Tinkerforge/evse-v2-bricklet/software/src/evse.c

/* evse-v2-bricklet
 * Copyright (C) 2021 Olaf Lüke <olaf@tinkerforge.com>
 *
 * evse.c: EVSE implementation
 *
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
 * You should have received a copy of the GNU Lesser General Public
 * License along with this library; if not, write to the
 * Free Software Foundation, Inc., 59 Temple Place - Suite 330,
 * Boston, MA 02111-1307, USA.
 */

#include "evse.h"

#include <float.h>

#include "configs/config_evse.h"
#include "bricklib2/hal/ccu4_pwm/ccu4_pwm.h"
#include "bricklib2/hal/system_timer/system_timer.h"
#include "bricklib2/logging/logging.h"
#include "bricklib2/utility/util_definitions.h"
#include "bricklib2/bootloader/bootloader.h"
#include "bricklib2/warp/meter.h"
#include "bricklib2/warp/contactor_check.h"

#include "adc.h"
#include "iec61851.h"
#include "lock.h"
#include "led.h"
#include "dc_fault.h"
#include "communication.h"
#include "charging_slot.h"
#include "button.h"
#include "iec61851.h"
#include "hardware_version.h"
#include "phase_control.h"
#include "ove_r37.h"

#include "xmc_scu.h"
#include "xmc_ccu4.h"
#include "xmc_vadc.h"
#include "xmc_gpio.h"

#define EVSE_RELAY_MONOFLOP_TIME 10000 // 10 seconds

EVSE evse;

static float last_duty_cycle = FLT_MAX;

// Interrupt for debugging
#if 0
#define evse_cp_pwm_irq IRQ_Hdlr_30
void __attribute__((optimize("-O3"))) __attribute__ ((section (".ram_code"))) evse_cp_pwm_irq(void) {
	XMC_VADC_GLOBAL_BackgroundTriggerConversion(VADC);
	XMC_GPIO_SetOutputHigh(EVSE_OUTPUT_GP_PIN);
}
#endif


void evse_set_output(const float cp_duty_cycle, const bool contactor) {
	static uint32_t last_resistance_counter_on_off = 0;
	static uint32_t last_resistance_counter_off_on = 0;
	evse_set_cp_duty_cycle(cp_duty_cycle);

	// If the contactor is to be enabled and the lock is currently
	// not completely closed, we start the locking procedure and return.
	// The contactor will only be enabled after the lock is closed.
#ifdef EVSE_LOCK_ENABLE
	if(contactor) {
		if(lock_get_state() != LOCK_STATE_CLOSE) {
			lock_set_locked(true);
			return;
		}
	}
#endif

	if(((bool)!XMC_GPIO_GetInput(EVSE_CONTACTOR_PIN)) != contactor) {
		if(((cp_duty_cycle == 0) || (cp_duty_cycle == 1000)) && (!contactor) && (last_resistance_counter_off_on == 0) && (last_resistance_counter_on_off == 0)) {
			// If the duty cycle is set to either 0% or 100% PWM and the contactor is supposed to be turned off,
			// it is possible that the WARP Charger wants to turn off the charging session while the car
			// still wants to charge. In this case we wait until the car actually stops charging and
			// changes the resistance back to 2700 ohm before we turn the contactor off.
			// This assures that the contactor is not switched under load.
			//
			// NOTE: In case of an emergency (for example a dc fault detection) the contactor is of course switched off
			//       immediately and directly in the fault detection code without any regard to charging-state,
			//       PWM value, resistance or similar.
			//       This function is only called in non-emergency cases.

			if(adc_result.cp_pe_resistance <= iec61851_get_cp_resistance_threshold(IEC61851_STATE_B)) {
				if(evse.contactor_turn_off_time == 0) {
					evse.contactor_turn_off_time = system_timer_get_ms();
					return;
				} else if(system_timer_is_time_elapsed_ms(evse.contactor_turn_off_time, 6*1000)) {
					// The car has to respond within 3 seconds (see IEC 61851-1 standard table A.6 sequence 10.1).
					// But according to Table A.6 sequence 10.2 the EVSE shall wait 6 seconds to turn the contactor off
					// if the EV does not respond to the change in CP signal. So we wait for 6 seconds here.
					evse.contactor_turn_off_time = 0;
					evse.contactor_maybe_switched_under_load = true;
				} else {
					return;
				}
			} else {
				evse.contactor_turn_off_time = 0;
			}
		}

		if(contactor) {
			// Reset on->off counter
			last_resistance_counter_on_off = 0;

			// If we are asked to turn the contactor on, we first wait for the diode check to finish
			if(iec61851.diode_check_pending) {
				return;
			}
			// If we are asked to turn the contactor on, we want to see at least 500ms worth of adc measurements
			// in a row that supports this conclusion.
			// To do this the ADC code increases a counter every time a new CP/PE resistance is saved.
			// We expect to see 20 consecutive measurements, otherwise we don't turn the contactor on.
			// This is a generic method to ignore glitches that persist for only a few adc measurements.
			// According to IEC 61851-1 standard table A.6 sequence 4, the EVSE is allowed to take 3s for the transation,
			// so there is we are not acutally in a rush here.
			// Additionally, the new iX3 seems to have a feature where it applies the 880 Ohm resistance for about 250ms
			// before immediately going back to 2700 Ohm after a change from 1-phase to 3-phase.
			// We think the BMW tries to to wake up the ISO15118 stack of the EVSE according to
			// IEC 61851-1 table A.6 sequence 11 "EV signal to the EV supply equipment".
			// We don't want to turn the contactor on/off in this case...
			if(last_resistance_counter_off_on == 0) {
				last_resistance_counter_off_on = adc_result.resistance_counter;
				return;
			} else if((uint32_t)(adc_result.resistance_counter - last_resistance_counter_off_on) < 19) { // 19 here is correct, one measurement was alredy done when we reach here
				// We have seen the resistance that results in a off -> on transtion for less than 20 measurements (500ms).
				return;
			} else {
				last_resistance_counter_off_on = 0;
			}
		} else {
			// Reset off->on counter
			last_resistance_counter_off_on = 0;

			// When we turn the contactor off, we need to react in a maximum of 100ms as defined in
			// IEC 61851-1 standard table A.6 sequence 8.1.
			if(last_resistance_counter_on_off == 0) {
				last_resistance_counter_on_off = adc_result.resistance_counter;
				return;
			} else if((uint32_t)(adc_result.resistance_counter - last_resistance_counter_on_off) < 2) { // 2 here is correct, one measurement was alredy done when we reach here
				// We have seen the resistance that results in a off -> on transtion for less than 3 measurements (75ms).
				return;
			} else {
				last_resistance_counter_on_off = 0;
			}
		}
		// Ignore all ADC measurements for a while if the contactor is
		// switched on or off, to be sure that the resulting EMI spike does
		// not give us a wrong measurement.
		adc_ignore_results(8);

		// Also ignore contactor check for a while when contactor changes state
		contactor_check.invalid_counter = MAX(5, contactor_check.invalid_counter);

		if(contactor) {
			// As soon as the contactor is turned on, we are not allowed to switch phases anymore until the car is disconnected.
			iec61851.instant_phase_switch_allowed = false;

			// Reset the "maybe switched under load" flag
			evse.contactor_maybe_switched_under_load = false;

			XMC_GPIO_SetOutputLow(EVSE_CONTACTOR_PIN);
		} else {
			XMC_GPIO_SetOutputHigh(EVSE_CONTACTOR_PIN);
		}

		evse.last_contactor_switch = system_timer_get_ms();
	}

#ifdef EVSE_LOCK_ENABLE
	if(!contactor) {
		if(lock_get_state() != LOCK_STATE_OPEN) {
			lock_set_locked(false);
		}
	}
#endif
}

void evse_load_config(void) {
	uint32_t page[EEPROM_PAGE_SIZE/sizeof(uint32_t)];
	bootloader_read_eeprom_page(EVSE_CONFIG_PAGE, page);

	// The magic number is not where it is supposed to be.
	// This is either our first startup or something went wrong.
	// We initialize the config data with sane default values.
	if(page[EVSE_CONFIG_MAGIC_POS] != EVSE_CONFIG_MAGIC) {
		evse.legacy_managed               = false;
		meter.relative_energy_sum.f       = 0.0f;
		evse.shutdown_input_configuration_old = hardware_version.is_v2 ? EVSE_V2_SHUTDOWN_INPUT_IGNORED : EVSE_V2_SHUTDOWN_INPUT_4200_WATT_ON_CLOSE;
	} else {
		evse.legacy_managed               = page[EVSE_CONFIG_MANAGED_POS];
		meter.relative_energy_sum.data    = page[EVSE_CONFIG_REL_SUM_POS];
		evse.shutdown_input_configuration_old = page[EVSE_CONFIG_SHUTDOWN_INPUT_POS];
	}

	if(page[EVSE_CONFIG_MAGIC2_POS] != EVSE_CONFIG_MAGIC2) {
		evse.input_configuration          = 0;
		evse.output_configuration         = EVSE_V2_OUTPUT_HIGH_IMPEDANCE;
		button.configuration              = EVSE_V2_BUTTON_CONFIGURATION_STOP_CHARGING;
	} else {
		evse.input_configuration          = page[EVSE_CONFIG_INPUT_POS];
		evse.output_configuration         = page[EVSE_CONFIG_OUTPUT_POS];
		button.configuration              = page[EVSE_CONFIG_BUTTON_POS];
	}

	if(page[EVSE_CONFIG_MAGIC3_POS] != EVSE_CONFIG_MAGIC3) {
		evse.boost_mode_enabled           = false;
		evse.ev_wakeup_enabled            = true;
	} else {
		evse.boost_mode_enabled           = page[EVSE_CONFIG_BOOST_POS];
		evse.ev_wakeup_enabled            = page[EVSE_CONFIG_EV_WAKUEP_POS];
	}

	if(page[EVSE_CONFIG_MAGIC4_POS] != EVSE_CONFIG_MAGIC4) {
		meter.relative_energy_import.f    = 0.0f;
		meter.relative_energy_export.f    = 0.0f;
	} else {
		meter.relative_energy_import.data = page[EVSE_CONFIG_REL_IMPORT_POS];
		meter.relative_energy_export.data = page[EVSE_CONFIG_REL_EXPORT_POS];
	}

	if(page[EVSE_CONFIG_MAGIC5_POS] != EVSE_CONFIG_MAGIC5) {
		phase_control.autoswitch_enabled = true;
		phase_control.phases_connected   = 3;
	} else {
		phase_control.autoswitch_enabled = page[EVSE_CONFIG_AUTOSWITCH_POS];
		phase_control.phases_connected   = (page[EVSE_CONFIG_PHASES_CON_POS] == 1) ? 1 : 3;
	}

	bool external_control_slot_to_default = false;
	// We use MAGIC6 to check if the new handling for external control is already active.
	// If the magic is not set, we activate the external control slot and set proper default values.
	// After that we set the new magic, so this only happens after first update.
	if(page[EVSE_CONFIG_MAGIC6_POS] != EVSE_CONFIG_MAGIC6) {
		external_control_slot_to_default = true;
	}

	if(page[EVSE_CONFIG_MAGIC7_POS] != EVSE_CONFIG_MAGIC7) {
		phase_control.phase_switch_wait_time = EVSE_V2_PHASE_SWITCH_WAIT_TIME_DEFAULT;
	} else {
		phase_control.phase_switch_wait_time = page[EVSE_CONFIG_PS_WAIT_TIME_POS];
	}

	if(page[EVSE_CONFIG_MAGIC8_POS] != EVSE_CONFIG_MAGIC8) {
		evse.shutdown_input_configuration = evse.shutdown_input_configuration_old;
	} else {
		evse.shutdown_input_configuration = page[EVSE_CONFIG_SHUTDOWN_INPUT2_POS];
	}

	if(page[EVSE_CONFIG_MAGIC9_POS] == EVSE_CONFIG_MAGIC9) {
		ove_r37.enabled                   = page[EVSE_CONFIG_OVE_R37_ENABLED_POS];
		ove_r37.undervoltage_threshold_pu = page[EVSE_CONFIG_OVE_R37_UV_THRESHOLD_POS];
		ove_r37.undervoltage_observe_ms   = page[EVSE_CONFIG_OVE_R37_UV_OBSERVE_POS];
		ove_r37.reconnect_wait_s          = page[EVSE_CONFIG_OVE_R37_RECONNECT_WAIT_POS];
	}

	// Handle charging slot defaults
	EVSEChargingSlotDefault *slot_default = (EVSEChargingSlotDefault *)(&page[EVSE_CONFIG_SLOT_DEFAULT_POS]);
	if(slot_default->magic == EVSE_CONFIG_SLOT_MAGIC) {
		for(uint8_t i = 0; i < 18; i++) {
			charging_slot.max_current_default[i]         = slot_default->current[i];
			charging_slot.active_default[i]              = slot_default->active_clear[i] & 1;
			charging_slot.clear_on_disconnect_default[i] = slot_default->active_clear[i] & 2;
		}
	} else {
		// If there is no default the button slot is activated and everything else is deactivated
		for(uint8_t i = 0; i < 18; i++) {
			charging_slot.max_current_default[i]         = 32000;
			charging_slot.active_default[i]              = false;
			charging_slot.clear_on_disconnect_default[i] = false;
		}

		// The default indices are offset by 2 to the slot indices
		charging_slot.max_current_default[CHARGING_SLOT_BUTTON-2]         = 32000;
		charging_slot.active_default[CHARGING_SLOT_BUTTON-2]              = true;
		charging_slot.clear_on_disconnect_default[CHARGING_SLOT_BUTTON-2] = false;

		charging_slot.max_current_default[CHARGING_SLOT_LOAD_MANAGEMENT-2]         = 0;
		charging_slot.active_default[CHARGING_SLOT_LOAD_MANAGEMENT-2]              = evse.legacy_managed;
		charging_slot.clear_on_disconnect_default[CHARGING_SLOT_LOAD_MANAGEMENT-2] = evse.legacy_managed;
	}

	if(external_control_slot_to_default) {
		charging_slot.max_current_default[CHARGING_SLOT_EXTERNAL-2]         = 32000;
		charging_slot.active_default[CHARGING_SLOT_EXTERNAL-2]              = false;
		charging_slot.clear_on_disconnect_default[CHARGING_SLOT_EXTERNAL-2] = false;
	}

	logd("Load config:\n\r");
	logd(" * legacy managed    %d\n\r", evse.legacy_managed);
	logd(" * relener           %d %d %d\n\r", meter.relative_energy_sum.data, meter.relative_energy_import.data, meter.relative_energy_export.data);
	logd(" * shutdown input    %d\n\r", evse.shutdown_input_configuration);
	logd(" * slot current      %d %d %d %d %d %d %d %d\n\r", charging_slot.max_current_default[0], charging_slot.max_current_default[1], charging_slot.max_current_default[2], charging_slot.max_current_default[3], charging_slot.max_current_default[4], charging_slot.max_current_default[5], charging_slot.max_current_default[6], charging_slot.max_current_default[7]);
	logd(" * slot active/clear %d %d %d %d %d %d %d %d\n\r", charging_slot.clear_on_disconnect_default[0], charging_slot.clear_on_disconnect_default[1], charging_slot.clear_on_disconnect_default[2], charging_slot.clear_on_disconnect_default[3], charging_slot.clear_on_disconnect_default[4], charging_slot.clear_on_disconnect_default[5], charging_slot.clear_on_disconnect_default[6], charging_slot.clear_on_disconnect_default[7]);
}

void evse_save_config(void) {
	// In old firmwares the page buffer is not zeroed.
	// If we downgrade from this firmware to an old firmware we were able to reproducible
	// get the "EVSE_CONFIG_MAGIC8" in the correct page index as uninitialized stack memory.
	// We put a new value above the page and print it (so the compiler can't possibly remove it),
	// to make sure that we can't accidentially leak the magic from a new firmware into an firmware.
	uint8_t random_val = system_timer_get_ms() % 255;
	uint32_t page[EEPROM_PAGE_SIZE/sizeof(uint32_t)] = {0};
	logd("random_val %d\n\r", random_val);

	page[EVSE_CONFIG_MAGIC_POS]           = EVSE_CONFIG_MAGIC;
	page[EVSE_CONFIG_MANAGED_POS]         = evse.legacy_managed;
	page[EVSE_CONFIG_SHUTDOWN_INPUT_POS]  = evse.shutdown_input_configuration_old;
	if(meter.reset_energy_meter) {
		page[EVSE_CONFIG_REL_SUM_POS]     = meter_register_set.EnergyActiveLSumImExSum.data;
		page[EVSE_CONFIG_REL_IMPORT_POS]  = meter_register_set.EnergyActiveLSumImport.data;
		page[EVSE_CONFIG_REL_EXPORT_POS]  = meter_register_set.EnergyActiveLSumExport.data;
		meter.relative_energy_sum.data    = meter_register_set.EnergyActiveLSumImExSum.data;
		meter.relative_energy_import.data = meter_register_set.EnergyActiveLSumImport.data;
		meter.relative_energy_export.data = meter_register_set.EnergyActiveLSumExport.data;
	} else {
		page[EVSE_CONFIG_REL_SUM_POS]     = meter.relative_energy_sum.data;
		page[EVSE_CONFIG_REL_IMPORT_POS]  = meter.relative_energy_import.data;
		page[EVSE_CONFIG_REL_EXPORT_POS]  = meter.relative_energy_export.data;
	}
	meter.reset_energy_meter = false;

	page[EVSE_CONFIG_MAGIC2_POS]          = EVSE_CONFIG_MAGIC2;
	page[EVSE_CONFIG_INPUT_POS]           = evse.input_configuration;
	page[EVSE_CONFIG_OUTPUT_POS]          = evse.output_configuration;
	page[EVSE_CONFIG_BUTTON_POS]          = button.configuration;

	page[EVSE_CONFIG_MAGIC3_POS]          = EVSE_CONFIG_MAGIC3;
	page[EVSE_CONFIG_BOOST_POS]           = evse.boost_mode_enabled;
	page[EVSE_CONFIG_EV_WAKUEP_POS]       = evse.ev_wakeup_enabled;

	page[EVSE_CONFIG_MAGIC4_POS]          = EVSE_CONFIG_MAGIC4;

	page[EVSE_CONFIG_MAGIC5_POS]          = EVSE_CONFIG_MAGIC5;
	page[EVSE_CONFIG_AUTOSWITCH_POS]      = phase_control.autoswitch_enabled;
	page[EVSE_CONFIG_PHASES_CON_POS]      = phase_control.phases_connected;

	page[EVSE_CONFIG_MAGIC6_POS]          = EVSE_CONFIG_MAGIC6;

	page[EVSE_CONFIG_MAGIC7_POS]          = EVSE_CONFIG_MAGIC7;
	page[EVSE_CONFIG_PS_WAIT_TIME_POS]    = phase_control.phase_switch_wait_time;

	page[EVSE_CONFIG_MAGIC8_POS]          = EVSE_CONFIG_MAGIC8;
	page[EVSE_CONFIG_SHUTDOWN_INPUT2_POS] = evse.shutdown_input_configuration;

	page[EVSE_CONFIG_MAGIC9_POS]                 = EVSE_CONFIG_MAGIC9;
	page[EVSE_CONFIG_OVE_R37_ENABLED_POS]        = ove_r37.enabled;
	page[EVSE_CONFIG_OVE_R37_UV_THRESHOLD_POS]   = ove_r37.undervoltage_threshold_pu;
	page[EVSE_CONFIG_OVE_R37_UV_OBSERVE_POS]     = ove_r37.undervoltage_observe_ms;
	page[EVSE_CONFIG_OVE_R37_RECONNECT_WAIT_POS] = ove_r37.reconnect_wait_s;
	page[EVSE_CONFIG_OVE_R37_START_DELAY_POS]    = 0;

	// Handle charging slot defaults
	EVSEChargingSlotDefault *slot_default = (EVSEChargingSlotDefault *)(&page[EVSE_CONFIG_SLOT_DEFAULT_POS]);
	for(uint8_t i = 0; i < 18; i++) {
		slot_default->current[i]      = charging_slot.max_current_default[i];
		slot_default->active_clear[i] = (charging_slot.active_default[i] << 0) | (charging_slot.clear_on_disconnect_default[i] << 1);
	}
	slot_default->magic = EVSE_CONFIG_SLOT_MAGIC;

	bootloader_write_eeprom_page(EVSE_CONFIG_PAGE, page);
}

void evse_factory_reset(void) {
	uint32_t page[EEPROM_PAGE_SIZE/sizeof(uint32_t)] = {0};
	bootloader_write_eeprom_page(EVSE_CONFIG_PAGE, page);

	NVIC_SystemReset();
}

uint16_t evse_get_cp_pwm_duty_cycle(void) {
	return XMC_CCU4_SLICE_GetTimerCompareMatch(hardware_version.is_v2 ? CCU40_CC40 : CCU41_CC40);
}

uint16_t evse_get_cp_duty_cycle(void) {
	if(iec61851.test_mode_no_pwm) {
		return (uint16_t)last_duty_cycle;
	}
	uint16_t duty_cycle = (uint16_t)((48000 - evse_get_cp_pwm_duty_cycle())/48.0 + 0.5);
	if((duty_cycle >= EVSE_BOOST_MODE_US) && (duty_cycle != 1000) && (duty_cycle != 0) && evse.boost_mode_enabled) {
		return duty_cycle - EVSE_BOOST_MODE_US;
	}

	return duty_cycle;
}

void evse_set_cp_duty_cycle(const float duty_cycle) {
	if(iec61851.test_mode_no_pwm) {
		last_duty_cycle = duty_cycle;
		return;
	}
	if(((last_duty_cycle == 1000)) && ((duty_cycle > 0) && (duty_cycle < 1000)) && (iec61851.charging_protocol != EVSE_V2_CHARGING_PROTOCOL_ISO15118)) {
		iec61851.state_b1b2_transition_seen = true;
	}
	if(last_duty_cycle != duty_cycle) {
		// Ignore ADC results for ~550ms after PWM change
		// We have seen in several hybrid BMW cars that they have a 2700 ohm resistance glitch on
		// the CP line after about 500ms after a change of the duty cycle....
		if((duty_cycle != 1000) && (duty_cycle != 0) && (last_duty_cycle != 1000) && (last_duty_cycle != 0)) {
			adc_ignore_results(22);
		}
		evse.last_duty_cycle_change_time = system_timer_get_ms();
		last_duty_cycle = duty_cycle;
	}

	// According to IEC 61851-1 table A.2 the duty cycle is allowed to be off by up to 5us.
	// If boost mode is enabled we add 4us to the duty cycle. This means that we are still within the standard.
	uint16_t adc_boost = 0;
	if((duty_cycle != 0) && (duty_cycle != 1000) && evse.boost_mode_enabled) {
		adc_boost = EVSE_BOOST_MODE_US;
	}

	// Note: We must not compare against evse_get_cp_pwm_duty_cycle() here to find out if
	// the compare value has to be updated. XMC_CCU4_SLICE_SetTimerCompareMatch() writes the
	// shadow register (CRS), while XMC_CCU4_SLICE_GetTimerCompareMatch() reads the active
	// register (CR), which is only updated on the next period match (up to 1ms later).
	static uint16_t last_written_cp_duty_cycle = 0xFFFF; // impossible value (valid range 0-48000)
	const uint16_t new_cp_duty_cycle = (uint16_t)(48000 - (duty_cycle + adc_boost)*48 + 0.5f);

	if(last_written_cp_duty_cycle != new_cp_duty_cycle) {
		last_written_cp_duty_cycle = new_cp_duty_cycle;

		adc_enable_all(duty_cycle > 999.99f);

		// EVSE V2 uses CCU40, EVSE V3 and V4 uses CCU41
		XMC_CCU4_SLICE_SetTimerCompareMatch(hardware_version.is_v2 ? CCU40_CC40 : CCU41_CC40, new_cp_duty_cycle);
		XMC_CCU4_EnableShadowTransfer(hardware_version.is_v2 ? CCU40 : CCU41, XMC_CCU4_SHADOW_TRANSFER_SLICE_0 | XMC_CCU4_SHADOW_TRANSFER_PRESCALER_SLICE_0);
	}
}

// Check pin header for max current
void evse_init_jumper(void) {
	const XMC_GPIO_CONFIG_t pin_config_input_tristate = {
		.mode             = XMC_GPIO_MODE_INPUT_TRISTATE,
		.input_hysteresis = XMC_GPIO_INPUT_HYSTERESIS_STANDARD
	};

	const XMC_GPIO_CONFIG_t pin_config_input_pullup = {
		.mode             = XMC_GPIO_MODE_INPUT_PULL_UP,
		.input_hysteresis = XMC_GPIO_INPUT_HYSTERESIS_STANDARD
	};

	const XMC_GPIO_CONFIG_t pin_config_input_pulldown = {
		.mode             = XMC_GPIO_MODE_INPUT_PULL_DOWN,
		.input_hysteresis = XMC_GPIO_INPUT_HYSTERESIS_STANDARD
	};

	XMC_GPIO_Init(EVSE_CONFIG_JUMPER_PIN0, &pin_config_input_pullup);
	XMC_GPIO_Init(EVSE_CONFIG_JUMPER_PIN1, &pin_config_input_pullup);
	system_timer_sleep_ms(50);
	bool pin0_pu = XMC_GPIO_GetInput(EVSE_CONFIG_JUMPER_PIN0);
	bool pin1_pu = XMC_GPIO_GetInput(EVSE_CONFIG_JUMPER_PIN1);

	XMC_GPIO_Init(EVSE_CONFIG_JUMPER_PIN0, &pin_config_input_pulldown);
	XMC_GPIO_Init(EVSE_CONFIG_JUMPER_PIN1, &pin_config_input_pulldown);
	system_timer_sleep_ms(50);
	bool pin0_pd = XMC_GPIO_GetInput(EVSE_CONFIG_JUMPER_PIN0);
	bool pin1_pd = XMC_GPIO_GetInput(EVSE_CONFIG_JUMPER_PIN1);

	XMC_GPIO_Init(EVSE_CONFIG_JUMPER_PIN0, &pin_config_input_tristate);
	XMC_GPIO_Init(EVSE_CONFIG_JUMPER_PIN1, &pin_config_input_tristate);

	// Differentiate between high, low and open
	char pin0 = 'x';
	if(pin0_pu && !pin0_pd) {
		pin0 = 'o';
	} else if(pin0_pu && pin0_pd) {
		pin0 = 'h';
	} else if(!pin0_pu && !pin0_pd) {
		pin0 = 'l';
	}

	char pin1 = 'x';
	if(pin1_pu && !pin1_pd) {
		pin1 = 'o';
	} else if(pin1_pu && pin1_pd) {
		pin1 = 'h';
	} else if(!pin1_pu && !pin1_pd) {
		pin1 = 'l';
	}

	if(hardware_version.is_v2) {
		if(pin0 == 'h' && pin1 == 'h') {
			evse.config_jumper_current = EVSE_CONFIG_JUMPER_RESERVED;
		} else if(pin0 == 'o' && pin1 == 'h') {
			evse.config_jumper_current = EVSE_CONFIG_JUMPER_CURRENT_32A;
		} else if(pin0 == 'l' && pin1 == 'h') {
			evse.config_jumper_current = EVSE_CONFIG_JUMPER_CURRENT_25A;
		} else if(pin0 == 'h' && pin1 == 'o') {
			evse.config_jumper_current = EVSE_CONFIG_JUMPER_CURRENT_20A;
		} else if(pin0 == 'o' && pin1 == 'o') {
			evse.config_jumper_current = EVSE_CONFIG_JUMPER_CURRENT_16A;
		} else if(pin0 == 'l' && pin1 == 'o') {
			evse.config_jumper_current = EVSE_CONFIG_JUMPER_CURRENT_13A;
		} else if(pin0 == 'h' && pin1 == 'l') {
			evse.config_jumper_current = EVSE_CONFIG_JUMPER_CURRENT_10A;
		} else if(pin0 == 'o' && pin1 == 'l') {
			evse.config_jumper_current = EVSE_CONFIG_JUMPER_CURRENT_6A;
		} else {
			evse.config_jumper_current = EVSE_CONFIG_JUMPER_UNCONFIGURED;
		}
	} else { // v3 or v4
		if(pin0 == 'h' && pin1 == 'h') {
			evse.config_jumper_current = EVSE_CONFIG_JUMPER_CURRENT_32A;
		} else if(pin0 == 'o' && pin1 == 'h') {
			evse.config_jumper_current = EVSE_CONFIG_JUMPER_RESERVED;
		} else if(pin0 == 'l' && pin1 == 'h') {
			evse.config_jumper_current = EVSE_CONFIG_JUMPER_CURRENT_25A;
		} else if(pin0 == 'h' && pin1 == 'o') {
			evse.config_jumper_current = EVSE_CONFIG_JUMPER_CURRENT_13A;
		} else if(pin0 == 'o' && pin1 == 'o') {
			evse.config_jumper_current = EVSE_CONFIG_JUMPER_UNCONFIGURED;
		} else if(pin0 == 'l' && pin1 == 'o') {
			evse.config_jumper_current = EVSE_CONFIG_JUMPER_CURRENT_6A;
		} else if(pin0 == 'h' && pin1 == 'l') {
			evse.config_jumper_current = EVSE_CONFIG_JUMPER_CURRENT_20A;
		} else if(pin0 == 'o' && pin1 == 'l') {
			evse.config_jumper_current = EVSE_CONFIG_JUMPER_CURRENT_10A;
		} else if(pin0 == 'l' && pin1 == 'l') {
			evse.config_jumper_current = EVSE_CONFIG_JUMPER_CURRENT_16A;
		} else {
			evse.config_jumper_current = EVSE_CONFIG_JUMPER_UNCONFIGURED;
		}
	}
}

// Use CCU40 slice 0 for CP/PE
// Use CCU40 slice 1 synchronously with slice 0 but with fixed duty-cycle
// Slice 1 is used to generate IRQ for ADC measurements to make sure that CP/PE PWM high level is measured at end of duty-cycle
void evse_v2_init_cp_pwm(void) {
	const XMC_CCU4_SLICE_COMPARE_CONFIG_t compare_config = {
		.timer_mode          = XMC_CCU4_SLICE_TIMER_COUNT_MODE_EA,
		.monoshot            = false,
		.shadow_xfer_clear   = 0,
		.dither_timer_period = 0,
		.dither_duty_cycle   = 0,
		.prescaler_mode      = XMC_CCU4_SLICE_PRESCALER_MODE_NORMAL,
		.mcm_enable          = 0,
		.prescaler_initval   = XMC_CCU4_SLICE_PRESCALER_2,
		.float_limit         = 0,
		.dither_limit        = 0,
		.passive_level       = XMC_CCU4_SLICE_OUTPUT_PASSIVE_LEVEL_LOW,
		.timer_concatenation = 0
	};

 	const XMC_CCU4_SLICE_EVENT_CONFIG_t event_config = {
		 .duration = XMC_CCU4_SLICE_EVENT_FILTER_5_CYCLES,
		 .edge = XMC_CCU4_SLICE_EVENT_EDGE_SENSITIVITY_RISING_EDGE,
		 .level = XMC_CCU4_SLICE_EVENT_LEVEL_SENSITIVITY_ACTIVE_HIGH,
		 .mapped_input = XMC_CCU4_SLICE_INPUT_AI
	};

	const XMC_GPIO_CONFIG_t gpio_out_config	= {
		.mode                = XMC_GPIO_MODE_OUTPUT_PUSH_PULL_ALT2,
		.input_hysteresis    = XMC_GPIO_INPUT_HYSTERESIS_STANDARD,
		.output_level        = XMC_GPIO_OUTPUT_LEVEL_LOW,
	};

	XMC_CCU4_Init(CCU40, XMC_CCU4_SLICE_MCMS_ACTION_TRANSFER_PR_CR);
	XMC_CCU4_StartPrescaler(CCU40);
	XMC_CCU4_SLICE_CompareInit(CCU40_CC40, &compare_config);
	XMC_CCU4_SLICE_CompareInit(CCU40_CC41, &compare_config);
	XMC_CCU4_SLICE_CompareInit(CCU40_CC42, &compare_config);

	// Set the period and compare register values
	XMC_CCU4_SLICE_SetTimerPeriodMatch(CCU40_CC40, EVSE_CP_PWM_PERIOD-1);
	XMC_CCU4_SLICE_SetTimerPeriodMatch(CCU40_CC41, EVSE_CP_PWM_PERIOD-1);
	XMC_CCU4_SLICE_SetTimerPeriodMatch(CCU40_CC42, EVSE_CP_PWM_PERIOD-1);
	XMC_CCU4_SLICE_SetTimerCompareMatch(CCU40_CC40, 48000 - 0*48);
	XMC_CCU4_SLICE_SetTimerCompareMatch(CCU40_CC41, 48000 - 30*48); // 3% duty-cycle (this puts the first ADC measurement at the end of the high part of the PWM)
	XMC_CCU4_SLICE_SetTimerCompareMatch(CCU40_CC42, 48000 - 750*48); // 75% duty-cycle (this puts the second ADC measurement at the middle the low part of the PWM)

	XMC_CCU4_EnableShadowTransfer(CCU40, XMC_CCU4_SHADOW_TRANSFER_SLICE_0 | XMC_CCU4_SHADOW_TRANSFER_PRESCALER_SLICE_0 | XMC_CCU4_SHADOW_TRANSFER_SLICE_1 | XMC_CCU4_SHADOW_TRANSFER_PRESCALER_SLICE_1 | XMC_CCU4_SHADOW_TRANSFER_SLICE_2 | XMC_CCU4_SHADOW_TRANSFER_PRESCALER_SLICE_2);

	XMC_GPIO_Init(EVSE_CP_PWM_PIN, &gpio_out_config);

	XMC_CCU4_EnableClock(CCU40, 0);
	XMC_CCU4_EnableClock(CCU40, 1);
	XMC_CCU4_EnableClock(CCU40, 2);

	// Start CCU40 slice 0, 1 and 2 in sync.
	XMC_CCU4_SLICE_ConfigureEvent(CCU40_CC40, XMC_CCU4_SLICE_EVENT_1, &event_config);
	XMC_CCU4_SLICE_ConfigureEvent(CCU40_CC41, XMC_CCU4_SLICE_EVENT_1, &event_config);
	XMC_CCU4_SLICE_ConfigureEvent(CCU40_CC42, XMC_CCU4_SLICE_EVENT_1, &event_config);
	XMC_CCU4_SLICE_StartConfig(CCU40_CC40, XMC_CCU4_SLICE_EVENT_1, XMC_CCU4_SLICE_START_MODE_TIMER_START_CLEAR);
	XMC_CCU4_SLICE_StartConfig(CCU40_CC41, XMC_CCU4_SLICE_EVENT_1, XMC_CCU4_SLICE_START_MODE_TIMER_START_CLEAR);
	XMC_CCU4_SLICE_StartConfig(CCU40_CC42, XMC_CCU4_SLICE_EVENT_1, XMC_CCU4_SLICE_START_MODE_TIMER_START_CLEAR);
	XMC_SCU_SetCcuTriggerHigh(SCU_GENERAL_CCUCON_GSC40_Msk);

	// Enable interrupt for CP PWM (on slice 1)
	XMC_CCU4_SLICE_EnableEvent(CCU40_CC41, XMC_CCU4_SLICE_IRQ_ID_COMPARE_MATCH_UP);
	XMC_CCU4_SLICE_SetInterruptNode(CCU40_CC41, XMC_CCU4_SLICE_IRQ_ID_COMPARE_MATCH_UP, XMC_CCU4_SLICE_SR_ID_2);

	// Enable interrupt for CP PWM (on slice 2)
	XMC_CCU4_SLICE_EnableEvent(CCU40_CC42, XMC_CCU4_SLICE_IRQ_ID_COMPARE_MATCH_UP);
	XMC_CCU4_SLICE_SetInterruptNode(CCU40_CC42, XMC_CCU4_SLICE_IRQ_ID_COMPARE_MATCH_UP, XMC_CCU4_SLICE_SR_ID_2);

	evse_set_cp_duty_cycle(1000.0);

	// Interrupt for debugging, uncomment if needed
//	NVIC_SetPriority(30, 1);
//	XMC_SCU_SetInterruptControl(30, XMC_SCU_IRQCTRL_CCU40_SR2_IRQ30);
//	NVIC_EnableIRQ(30);
}

void evse_v3_init_cp_pwm(void) {
	const XMC_CCU4_SLICE_COMPARE_CONFIG_t compare_config = {
		.timer_mode          = XMC_CCU4_SLICE_TIMER_COUNT_MODE_EA,
		.monoshot            = false,
		.shadow_xfer_clear   = 0,
		.dither_timer_period = 0,
		.dither_duty_cycle   = 0,
		.prescaler_mode      = XMC_CCU4_SLICE_PRESCALER_MODE_NORMAL,
		.mcm_enable          = 0,
		.prescaler_initval   = XMC_CCU4_SLICE_PRESCALER_2,
		.float_limit         = 0,
		.dither_limit        = 0,
		.passive_level       = XMC_CCU4_SLICE_OUTPUT_PASSIVE_LEVEL_LOW,
		.timer_concatenation = 0
	};

 	const XMC_CCU4_SLICE_EVENT_CONFIG_t event_config = {
		 .duration = XMC_CCU4_SLICE_EVENT_FILTER_5_CYCLES,
		 .edge = XMC_CCU4_SLICE_EVENT_EDGE_SENSITIVITY_RISING_EDGE,
		 .level = XMC_CCU4_SLICE_EVENT_LEVEL_SENSITIVITY_ACTIVE_HIGH,
		 .mapped_input = XMC_CCU4_SLICE_INPUT_AI
	};

	const XMC_GPIO_CONFIG_t gpio_out_config	= {
		.mode                = XMC_GPIO_MODE_OUTPUT_PUSH_PULL_ALT9,
		.input_hysteresis    = XMC_GPIO_INPUT_HYSTERESIS_STANDARD,
		.output_level        = XMC_GPIO_OUTPUT_LEVEL_LOW,
	};

	XMC_CCU4_Init(CCU41, XMC_CCU4_SLICE_MCMS_ACTION_TRANSFER_PR_CR);
	XMC_CCU4_StartPrescaler(CCU41);
	XMC_CCU4_SLICE_CompareInit(CCU41_CC40, &compare_config);
	XMC_CCU4_SLICE_CompareInit(CCU41_CC41, &compare_config);
	XMC_CCU4_SLICE_CompareInit(CCU41_CC42, &compare_config);

	// Set the period and compare register values
	XMC_CCU4_SLICE_SetTimerPeriodMatch(CCU41_CC40, EVSE_CP_PWM_PERIOD-1);
	XMC_CCU4_SLICE_SetTimerPeriodMatch(CCU41_CC41, EVSE_CP_PWM_PERIOD-1);
	XMC_CCU4_SLICE_SetTimerPeriodMatch(CCU41_CC42, EVSE_CP_PWM_PERIOD-1);
	XMC_CCU4_SLICE_SetTimerCompareMatch(CCU41_CC40, 48000 - 0*48);
	XMC_CCU4_SLICE_SetTimerCompareMatch(CCU41_CC41, 48000 - 30*48); // 3% duty-cycle (this puts the first ADC measurement at the end of the high part of the PWM)
	XMC_CCU4_SLICE_SetTimerCompareMatch(CCU41_CC42, 48000 - 750*48); // 75% duty-cycle (this puts the second ADC measurement at the middle the low part of the PWM)

	XMC_CCU4_EnableShadowTransfer(CCU41, XMC_CCU4_SHADOW_TRANSFER_SLICE_0 | XMC_CCU4_SHADOW_TRANSFER_PRESCALER_SLICE_0 | XMC_CCU4_SHADOW_TRANSFER_SLICE_1 | XMC_CCU4_SHADOW_TRANSFER_PRESCALER_SLICE_1 | XMC_CCU4_SHADOW_TRANSFER_SLICE_2 | XMC_CCU4_SHADOW_TRANSFER_PRESCALER_SLICE_2);

	XMC_GPIO_Init(EVSE_CP_PWM_PIN, &gpio_out_config);

	XMC_CCU4_EnableClock(CCU41, 0);
	XMC_CCU4_EnableClock(CCU41, 1);
	XMC_CCU4_EnableClock(CCU41, 2);

	// Start CCU41 slice 0, 1 and 2 in sync.
	XMC_CCU4_SLICE_ConfigureEvent(CCU41_CC40, XMC_CCU4_SLICE_EVENT_1, &event_config);
	XMC_CCU4_SLICE_ConfigureEvent(CCU41_CC41, XMC_CCU4_SLICE_EVENT_1, &event_config);
	XMC_CCU4_SLICE_ConfigureEvent(CCU41_CC42, XMC_CCU4_SLICE_EVENT_1, &event_config);
	XMC_CCU4_SLICE_StartConfig(CCU41_CC40, XMC_CCU4_SLICE_EVENT_1, XMC_CCU4_SLICE_START_MODE_TIMER_START_CLEAR);
	XMC_CCU4_SLICE_StartConfig(CCU41_CC41, XMC_CCU4_SLICE_EVENT_1, XMC_CCU4_SLICE_START_MODE_TIMER_START_CLEAR);
	XMC_CCU4_SLICE_StartConfig(CCU41_CC42, XMC_CCU4_SLICE_EVENT_1, XMC_CCU4_SLICE_START_MODE_TIMER_START_CLEAR);
	XMC_SCU_SetCcuTriggerHigh(SCU_GENERAL_CCUCON_GSC41_Msk);

	// Enable interrupt for CP PWM (on slice 1)
	XMC_CCU4_SLICE_EnableEvent(CCU41_CC41, XMC_CCU4_SLICE_IRQ_ID_COMPARE_MATCH_UP);
	XMC_CCU4_SLICE_SetInterruptNode(CCU41_CC41, XMC_CCU4_SLICE_IRQ_ID_COMPARE_MATCH_UP, XMC_CCU4_SLICE_SR_ID_2);

	// Enable interrupt for CP PWM (on slice 2)
	XMC_CCU4_SLICE_EnableEvent(CCU41_CC42, XMC_CCU4_SLICE_IRQ_ID_COMPARE_MATCH_UP);
	XMC_CCU4_SLICE_SetInterruptNode(CCU41_CC42, XMC_CCU4_SLICE_IRQ_ID_COMPARE_MATCH_UP, XMC_CCU4_SLICE_SR_ID_2);

	evse_set_cp_duty_cycle(1000.0);

	// Interrupt for debugging, uncomment if needed
//	NVIC_SetPriority(30, 1);
//	XMC_SCU_SetInterruptControl(30, XMC_SCU_IRQCTRL_CCU41_SR2_IRQ30);
//	NVIC_EnableIRQ(30);
}

bool evse_is_shutdown(void) {
	static bool last_return = false;
	static bool change_time = 0;

	bool new_return = false;
	if((evse.shutdown_input_configuration == EVSE_V2_SHUTDOWN_INPUT_SHUTDOWN_ON_CLOSE) || (evse.shutdown_input_configuration == EVSE_V2_SHUTDOWN_INPUT_4200_WATT_ON_CLOSE)) {
		if(!XMC_GPIO_GetInput(EVSE_SHUTDOWN_PIN)) {
			new_return = true;
		}
	} else if((evse.shutdown_input_configuration == EVSE_V2_SHUTDOWN_INPUT_SHUTDOWN_ON_OPEN) || (evse.shutdown_input_configuration == EVSE_V2_SHUTDOWN_INPUT_4200_WATT_ON_OPEN)) {
		if(XMC_GPIO_GetInput(EVSE_SHUTDOWN_PIN)) {
			new_return = true;
		}
	}

	// 10ms debounce
	if((new_return != last_return) && (change_time = 0)) {
		change_time = system_timer_get_ms();
		return last_return;
	} else if(new_return != last_return) {
		if(system_timer_is_time_elapsed_ms(change_time, 10)) {
			last_return = new_return;
			change_time = 0;
		} else {
			return last_return;
		}
	}

	return new_return;
}

void evse_cp_connect(void) {
	if(XMC_GPIO_GetInput(EVSE_CP_DISCONNECT_PIN)) {
		evse.cp_reconnect_time = system_timer_get_ms();
		// Don't allow 0, since we use it as flag for "re-connect time handled"
		if(evse.cp_reconnect_time == 0) {
			evse.cp_reconnect_time = UINT32_MAX;
		}
		adc_ignore_results(1);
	}
	XMC_GPIO_SetOutputLow(EVSE_CP_DISCONNECT_PIN);
}

void evse_cp_disconnect(void) {
	XMC_GPIO_SetOutputHigh(EVSE_CP_DISCONNECT_PIN);
}

bool evse_is_cp_connected(void) {
	// Add 75ms after cp is re-connected to make sure that at least one adc measurement has gone through
	if((evse.cp_reconnect_time != 0) && !system_timer_is_time_elapsed_ms(evse.cp_reconnect_time, 75)) {
		return false;
	}
	evse.cp_reconnect_time = 0;

	return !XMC_GPIO_GetInput(EVSE_CP_DISCONNECT_PIN);
}

void evse_init(void) {
	const XMC_GPIO_CONFIG_t pin_config_output_low = {
		.mode             = XMC_GPIO_MODE_OUTPUT_PUSH_PULL,
		.output_level     = XMC_GPIO_OUTPUT_LEVEL_LOW
	};

	const XMC_GPIO_CONFIG_t pin_config_output_high = {
		.mode             = XMC_GPIO_MODE_OUTPUT_PUSH_PULL,
		.output_level     = XMC_GPIO_OUTPUT_LEVEL_HIGH
	};

	const XMC_GPIO_CONFIG_t pin_config_input = {
		.mode             = XMC_GPIO_MODE_INPUT_TRISTATE,
		.input_hysteresis = XMC_GPIO_INPUT_HYSTERESIS_STANDARD
	};

	XMC_GPIO_Init(EVSE_CONTACTOR_PIN,     &pin_config_output_high);
	XMC_GPIO_Init(EVSE_CP_DISCONNECT_PIN, &pin_config_output_low);
	XMC_GPIO_Init(EVSE_SHUTDOWN_PIN,      &pin_config_input);

	if(hardware_version.is_v2) {
		evse_v2_init_cp_pwm();
		XMC_GPIO_Init(EVSE_INPUT_GP_PIN, &pin_config_input);
	} else if(hardware_version.is_v3 || hardware_version.is_v4) {
		evse_v3_init_cp_pwm();
	}

	evse.last_contactor_switch = system_timer_get_ms();
	evse.output_configuration = EVSE_V2_OUTPUT_HIGH_IMPEDANCE;
	evse.control_pilot_disconnect = false;
	evse.boost_mode_enabled = false;
	evse.ev_wakeup_enabled = true;
	evse.has_lock_switch = false;
	evse.cp_reconnect_time = 0;

	evse_load_config();

	// Support for gp output pin only in EVSE V2
	if(hardware_version.is_v2) {
		if(evse.output_configuration == EVSE_V2_OUTPUT_CONNECTED_TO_GROUND) {
			XMC_GPIO_Init(EVSE_OUTPUT_GP_PIN, &pin_config_output_high);
		} else if(evse.output_configuration == EVSE_V2_OUTPUT_HIGH_IMPEDANCE) {
			XMC_GPIO_Init(EVSE_OUTPUT_GP_PIN, &pin_config_output_low);
		}
	}

	evse_init_jumper();

	evse.startup_time = system_timer_get_ms();
	evse.factory_reset_time = 0;
	evse.car_stopped_charging = false;
	evse.communication_watchdog_time = 0;
	evse.contactor_turn_off_time = 0;
	evse.last_duty_cycle_change_time = 0;
}

void evse_tick_debug(void) {
#if LOGGING_LEVEL != LOGGING_NONE
	static uint32_t debug_time = 0;
	if(system_timer_is_time_elapsed_ms(debug_time, 250)) {
		debug_time = system_timer_get_ms();
		uartbb_printf("\n\r");
		uartbb_printf("IEC61851 State: %d\n\r", iec61851.state);
		uartbb_printf("Has lock switch: %d\n\r", evse.has_lock_switch);
		uartbb_printf("Jumper configuration: %d\n\r", evse.config_jumper_current);
		uartbb_printf("LED State: %d\n\r", led.state);
		uartbb_printf("Resistance: CP %d, PP %d\n\r", adc_result.cp_pe_resistance, adc_result.pp_pe_resistance);
		uartbb_printf("CP PWM duty cycle: %d\n\r", ccu4_pwm_get_duty_cycle(EVSE_CP_PWM_SLICE_NUMBER));
		uartbb_printf("Contactor Check: AC1 %d, AC2 %d, State: %d, Error: %d\n\r", contactor_check.ac1_edge_count, contactor_check.ac2_edge_count, contactor_check.state, contactor_check.error);
		if(hardware_version.is_v2) {
			uartbb_printf("GPIO: Input %d, Output %d\n\r", XMC_GPIO_GetInput(EVSE_INPUT_GP_PIN), XMC_GPIO_GetInput(EVSE_OUTPUT_GP_PIN));
		}
		uartbb_printf("Lock State: %d\n\r", lock.state);
	}
#endif
}

void evse_tick(void) {
	if(evse.startup_time != 0 && !system_timer_is_time_elapsed_ms(evse.startup_time, 1000)) {
		// Wait for 1s so everything can start/boot properly
		return;
	}

	if(evse.factory_reset_time != 0) {
		if(system_timer_is_time_elapsed_ms(evse.factory_reset_time, 500)) {
			evse_factory_reset();
		}
	}

	// Turn LED on (LED flicker off after startup/calibration)
	if(evse.startup_time != 0) {
		evse.startup_time = 0;

		// Start a dc fault module calibration on startup
		dc_fault.calibration_start = true;

		// Return to make sure that the dc fault tick is called at least once before the iec61851 tick.
		return;
	} else if(dc_fault.calibration_running) {
		// TODO: Just do nothing here, right?
		// LED flickering here would just be confusing, this is not an error state.
	} else {
		// Otherwise we implement the EVSE according to IEC 61851.
		iec61851_tick();
	}

	// Restart EVSE after 5 minutes without any communication with a Brick
	if((evse.communication_watchdog_time != 0) && system_timer_is_time_elapsed_ms(evse.communication_watchdog_time, 1000*60*5)) {
		// Only restart EVSE if brick-communication-watchdog triggers if no car is connected
		if(iec61851.state == IEC61851_STATE_A) {
			NVIC_SystemReset();
		}
	}

//	evse_tick_debug();
}
