Tinkerforge/evse-v2-bricklet/software/src/led.h

/* evse-v2-bricklet
 * Copyright (C) 2021 Olaf Lüke <olaf@tinkerforge.com>
 *
 * led.h: EVSE 2.0 LED driver
 *
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
 * You should have received a copy of the GNU Lesser General Public
 * License along with this library; if not, write to the
 * Free Software Foundation, Inc., 59 Temple Place - Suite 330,
 * Boston, MA 02111-1307, USA.
 */

#ifndef LED_H
#define LED_H

#include <stdint.h>
#include <stdbool.h>

#define LED_FLICKER_DURATION    50

#define LED_BLINK_DURATION_ON   250
#define LED_BLINK_DURATION_OFF  250
#define LED_BLINK_DURATION_WAIT 2000

#define LED_ENUMERATE_DURATION  2000UL
#define LED_ENUMERATE_BLINK_ON  250
#define LED_ENUMERATE_BLINK_OFF 250

#define LED_STANDBY_TIME (1000*60*15) // Standby after 15 minutes

#define LED_HUE_RED 0
#define LED_HUE_ORANGE 30
#define LED_HUE_YELLOW 60
#define LED_HUE_GRASS_GREEN 90
#define LED_HUE_GREEN 120
#define LED_HUE_SPRING_GREEN 150
#define LED_HUE_CYAN 180
#define LED_HUE_GREEN_BLUE 210
#define LED_HUE_BLUE 240
#define LED_HUE_VIOLET 270
#define LED_HUE_MAGENTA 300
#define LED_HUE_PURPLE 330

#define LED_HUE_BOOTING  LED_HUE_MAGENTA
#define LED_HUE_ERROR    LED_HUE_RED
#define LED_HUE_STANDARD LED_HUE_BLUE
#define LED_HUE_OK       LED_HUE_GREEN
#define LED_HUE_WARNING  LED_HUE_ORANGE

#define LED_ENUMERATOR_NUM 8

typedef enum {
	LED_STATE_OFF,
	LED_STATE_ON,
	LED_STATE_BLINKING,
	LED_STATE_FLICKER,
	LED_STATE_BREATHING,
	LED_STATE_API,
	LED_STATE_ENUMERATE
} LEDState;

typedef struct {
	LEDState state;

	uint32_t on_time;

	uint32_t blink_num;
	uint32_t blink_count;
	bool blink_on;
	uint32_t blink_last_time;
	int16_t blink_external;

	bool flicker_on;
	uint32_t flicker_last_time;

	uint32_t breathing_time;
	int16_t breathing_index;
	bool breathing_up;

	int16_t api_indication;
	uint16_t api_duration;
	uint32_t api_start;

	uint8_t api_ack_counter;
	uint8_t api_ack_index;
	uint32_t api_ack_time;

	uint8_t api_nack_counter;
	uint8_t api_nack_index;
	uint32_t api_nack_time;

	uint8_t api_nag_counter;
	uint8_t api_nag_index;
	uint32_t api_nag_time;

	bool currently_in_wait_state;

	uint16_t set_h;
	uint8_t set_s;
	uint8_t set_v;

	uint16_t h;
	uint8_t s;
	uint8_t v;
	uint8_t r;
	uint8_t g;
	uint8_t b;

	uint16_t enumerator_h[LED_ENUMERATOR_NUM];
	uint8_t enumerator_s[LED_ENUMERATOR_NUM];
	uint8_t enumerator_v[LED_ENUMERATOR_NUM];
	uint8_t enumerate_value;
	uint32_t enumerate_value_change_time;
	uint32_t enumerate_start_time;
	uint32_t enumerate_initial_time;
	LEDState enumerate_before_state;
} LED;

extern LED led;

void led_set_off(void);
void led_set_on(const bool force);
void led_set_blinking(const uint8_t num);
void led_set_breathing(void);
void led_set_enumerate(void);

void led_init(void);
void led_tick(void);

#endif
